vejja/radiateurs/hardware/pilote/IMG_2034.JPG

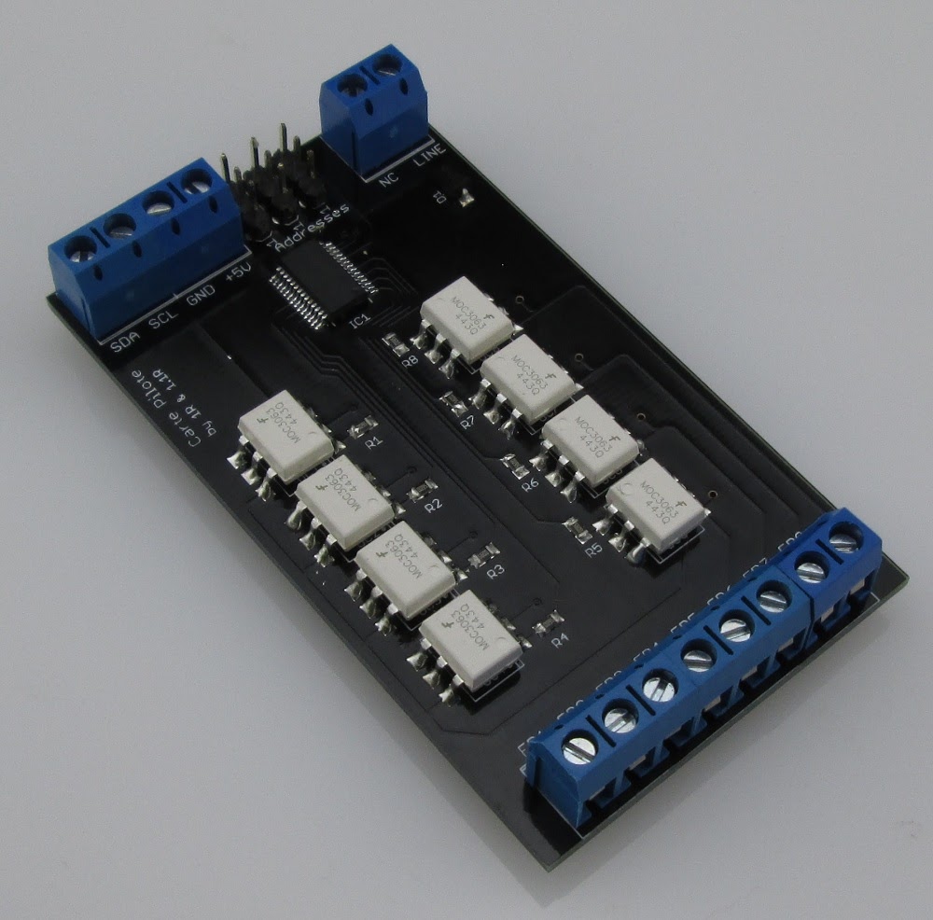
hardware/pilote/IMG_2034.JPG
