vejja/radiateurs/hardware/pilote/IMG_2054.JPG

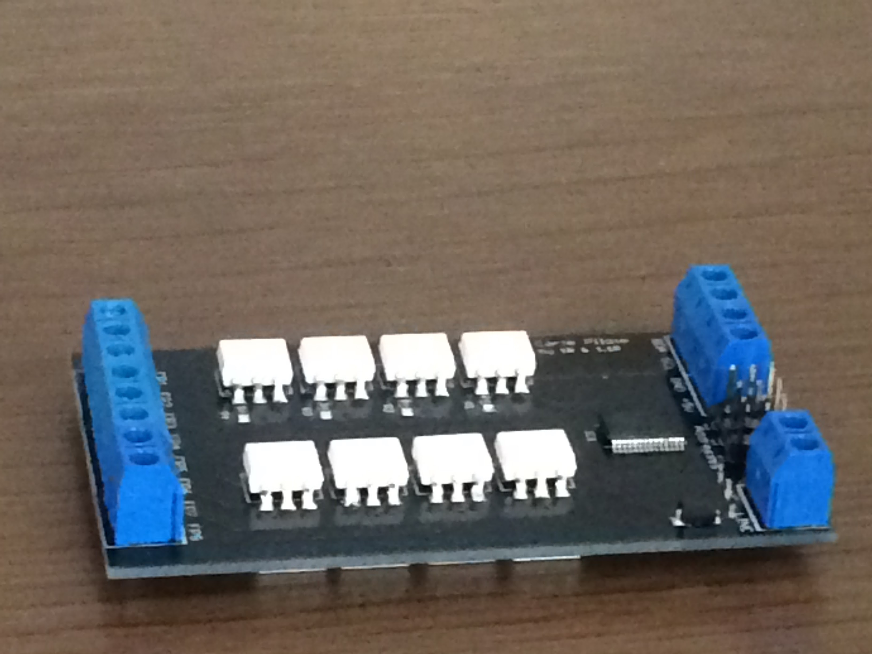
hardware/pilote/IMG_2054.JPG
